mohoyt/cyoa_ortho/firmware/cyoa_ortho/keymaps/vial-5x12-noencoder/config.h

#pragma once

#define VIAL_KEYBOARD_UID {0x49, 0x57, 0xBD, 0x3D, 0xC0, 0xA4, 0xF0, 0x3E}

/* #define ENCODERS_PAD { D3, D2 } */

#define VIAL_COMBO_ENTRIES 2
#define VIAL_TAP_DANCE_ENTRIES 4
#define VIAL_KEY_OVERRIDE_ENTRIES 2
#define DYNAMIC_KEYMAP_LAYER_COUNT 3
#define VIAL_UNLOCK_COMBO_ROWS { 0, 1 }
#define VIAL_UNLOCK_COMBO_COLS { 0, 1 }
/* #define VIAL_ENCODER_DEFAULT { KC_VOLD, KC_VOLU, KC_MPRV, KC_MNXT, KC_MPRV, KC_MNXT } */
